coconauts/watchduino2/docs/images/IMG_0070.JPG

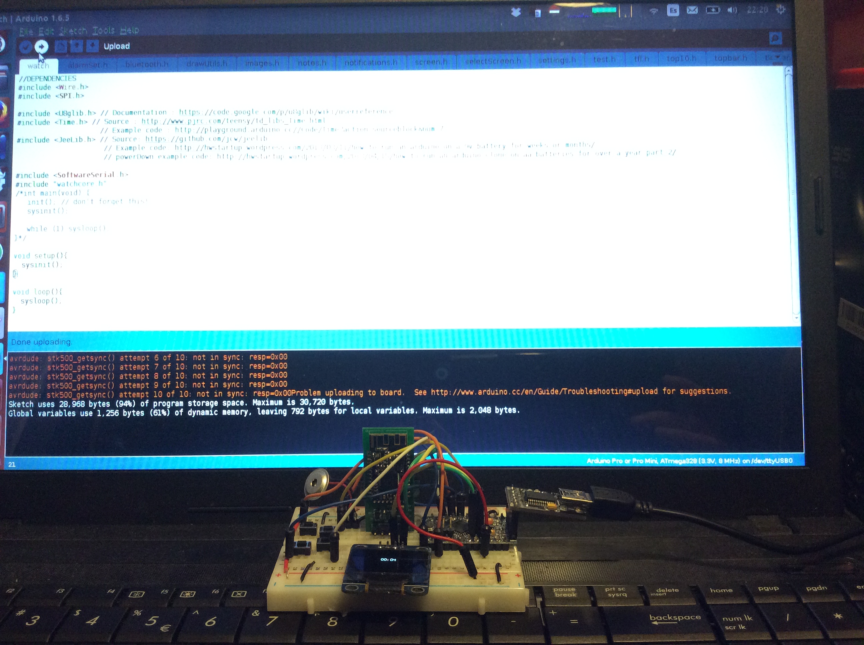
docs/images/IMG_0070.JPG
